jmos1/KEYPAD_V01/Outputs/Images/bottom.PNG

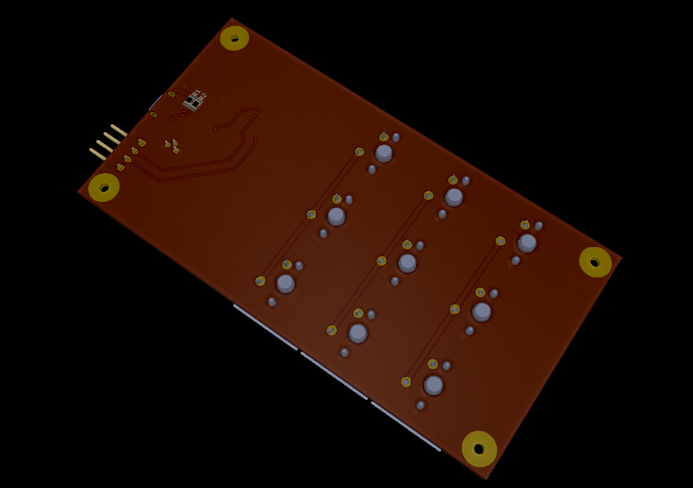
Outputs/Images/bottom.PNG
